raspibo/HotAirGun/Pict/HAG1.jpg

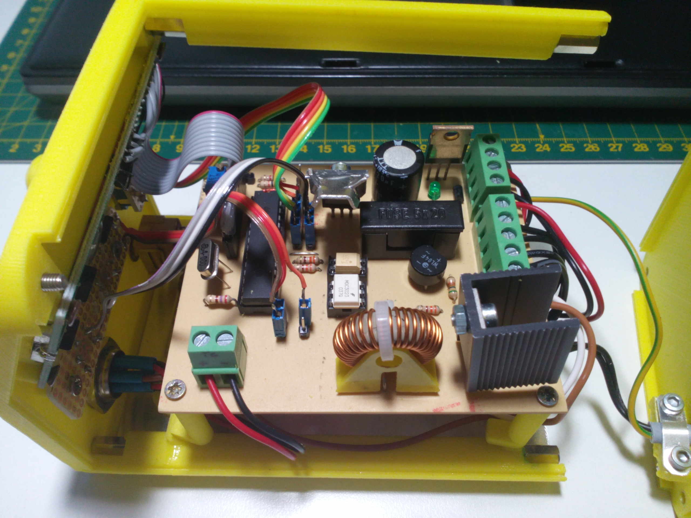
Pict/HAG1.jpg
