raspibo/HotAirGun/Pict/Sim.jpg

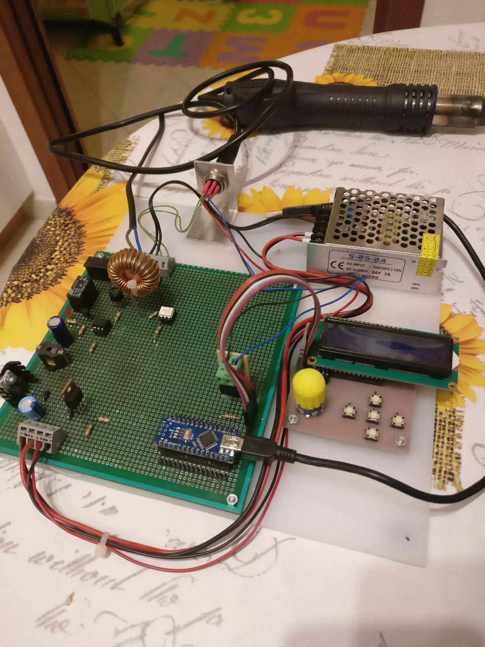
Pict/Sim.jpg
